Totof34/Bobineuse-V4-HMI/Images/DRV8825microstepmap.jpg

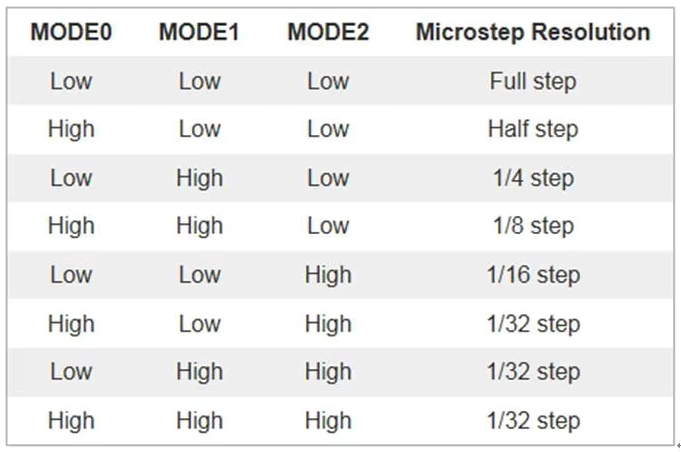
Images/DRV8825microstepmap.jpg
