Totof34/Bobineuse-V4-HMI/Nextion/Images HMI/Bobine_face.jpg

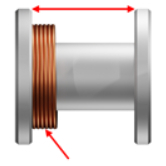
Nextion/Images HMI/Bobine_face.jpg
