Totof34/Bobineuse-V4-HMI/Nextion/Images HMI/Carcasse pour EI.jpg

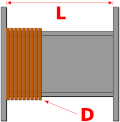
Nextion/Images HMI/Carcasse pour EI.jpg
